dudeku/esp-now-differential-probe/scripts/graphs/0_5_GeV.png

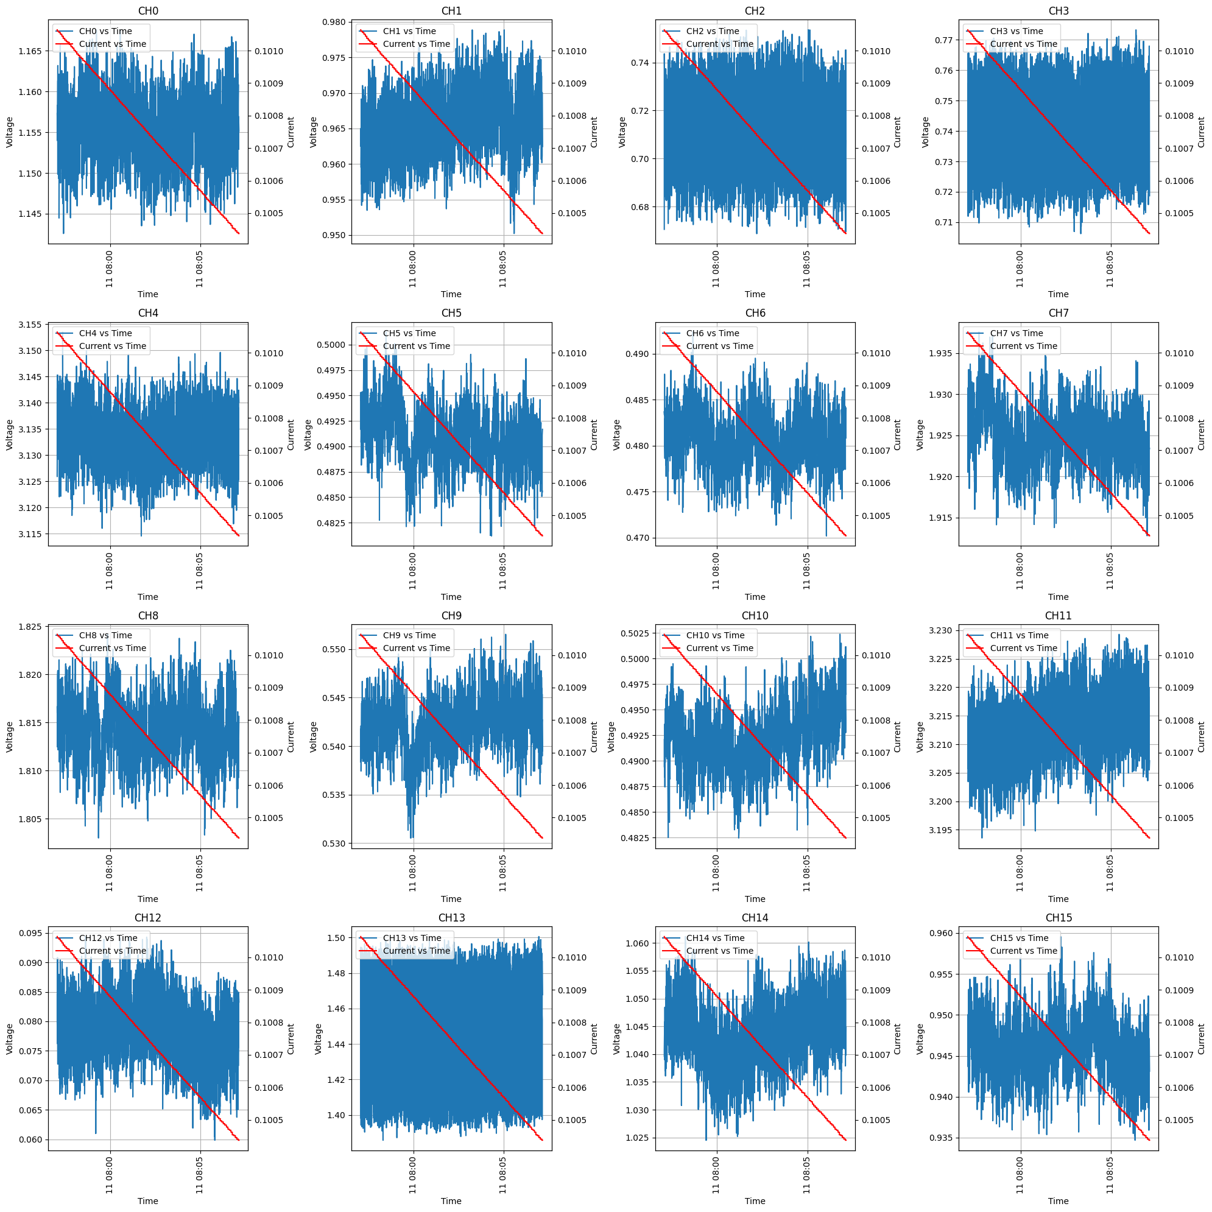
scripts/graphs/0_5_GeV.png
