dudeku/esp-now-differential-probe/scripts/graphs/espsonda_08-06-30_27-02-2025_1.png

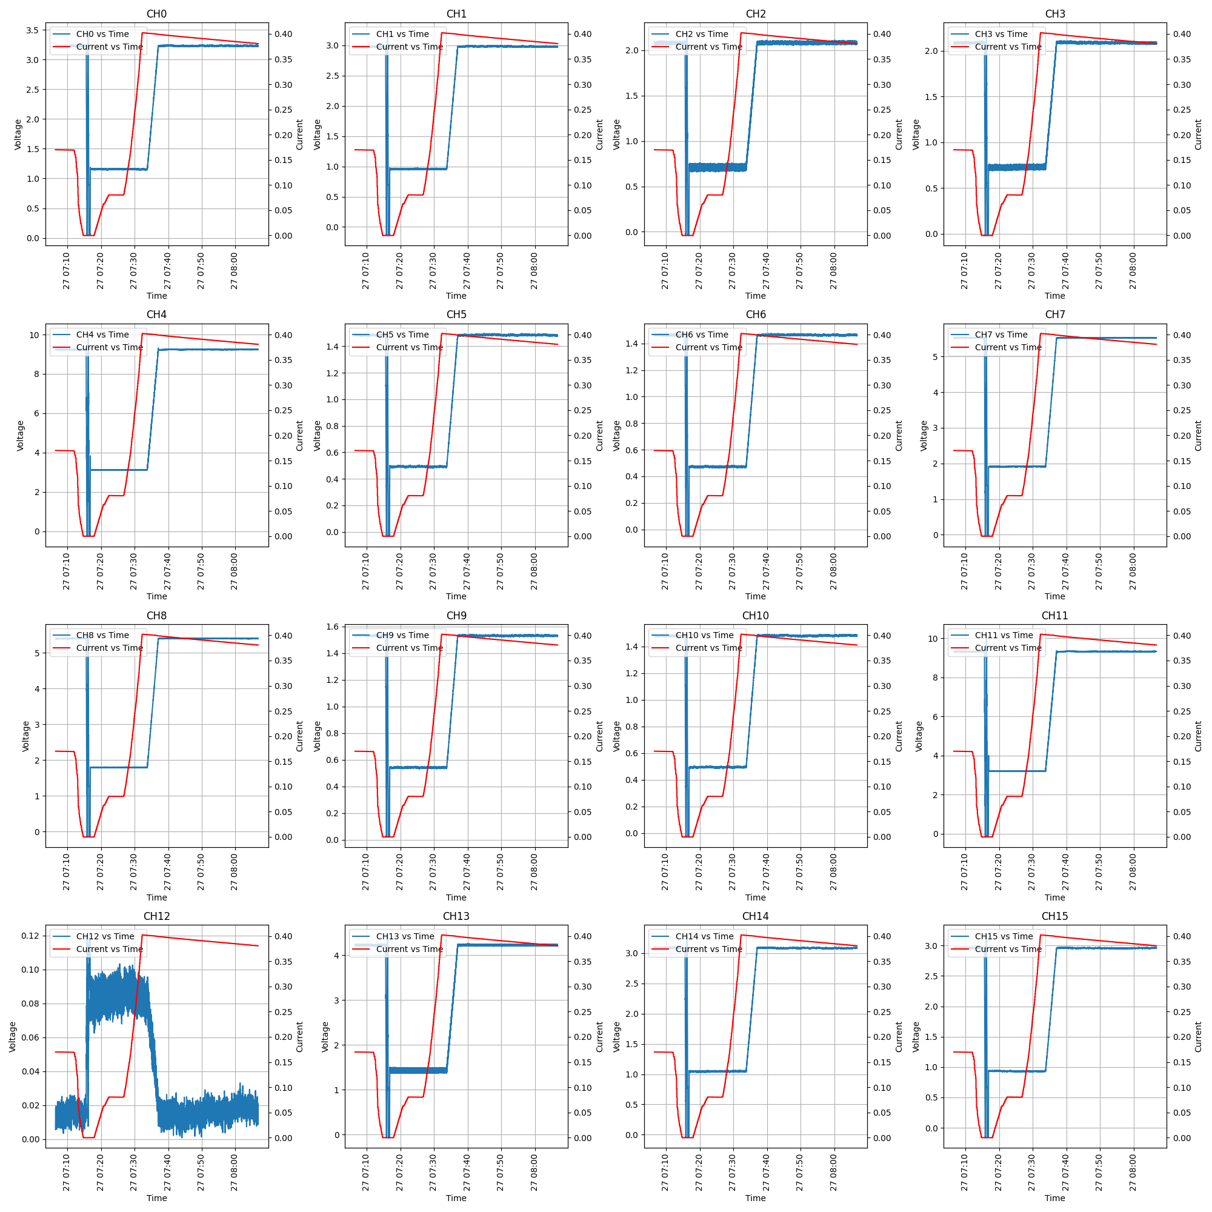
scripts/graphs/espsonda_08-06-30_27-02-2025_1.png
