dudeku/esp-now-differential-probe/scripts/graphs/espsonda_08-07-44_05-06-2025_2.png

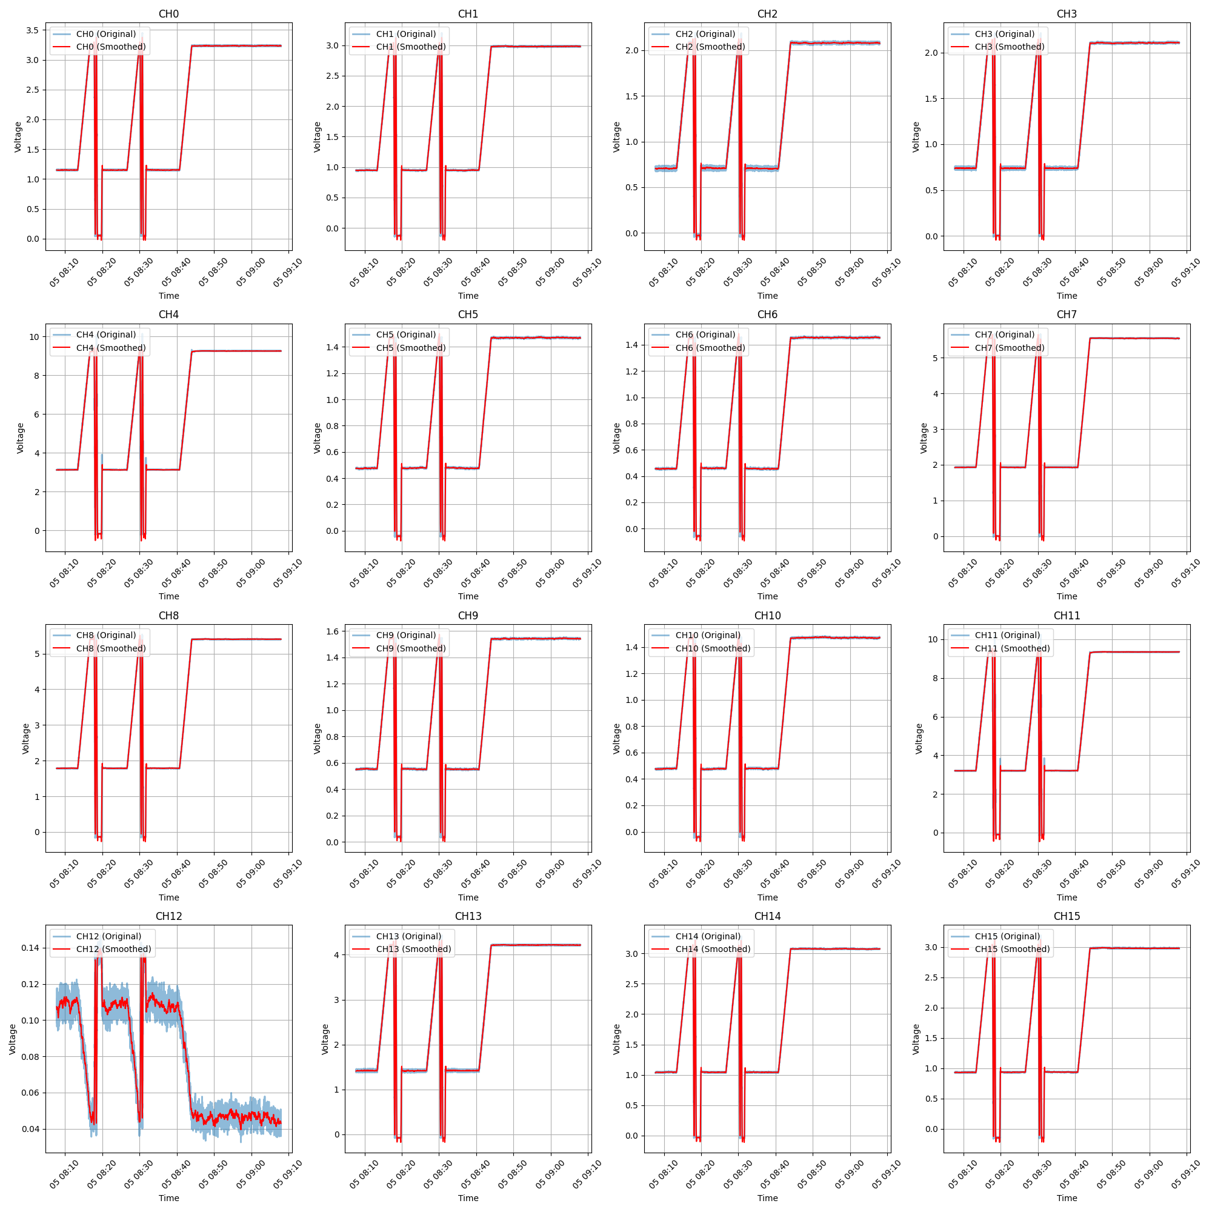
scripts/graphs/espsonda_08-07-44_05-06-2025_2.png
