dudeku/esp-now-differential-probe/scripts/graphs/espsonda_09-22-08_12-12-2025_fig3.png

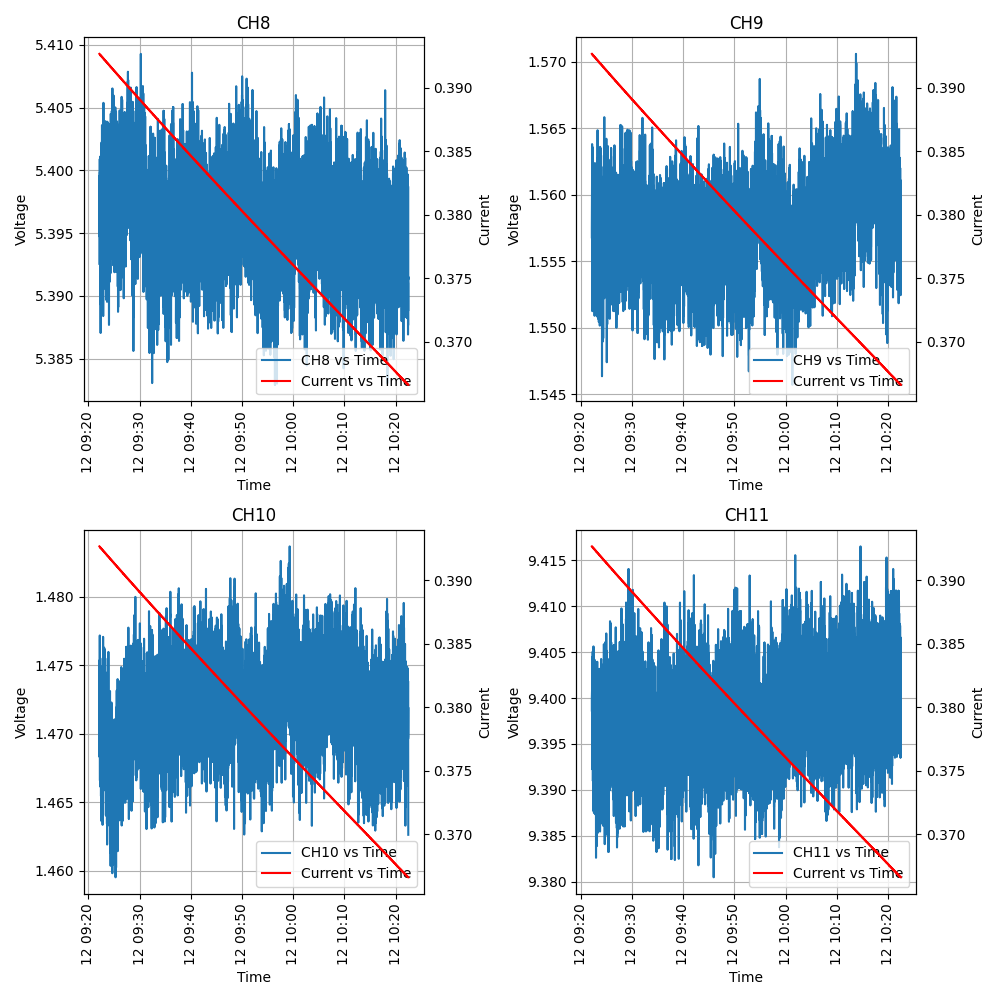
scripts/graphs/espsonda_09-22-08_12-12-2025_fig3.png
