dudeku/esp-now-differential-probe/scripts/graphs/espsonda_10-20-50_02-06-2025_2.png

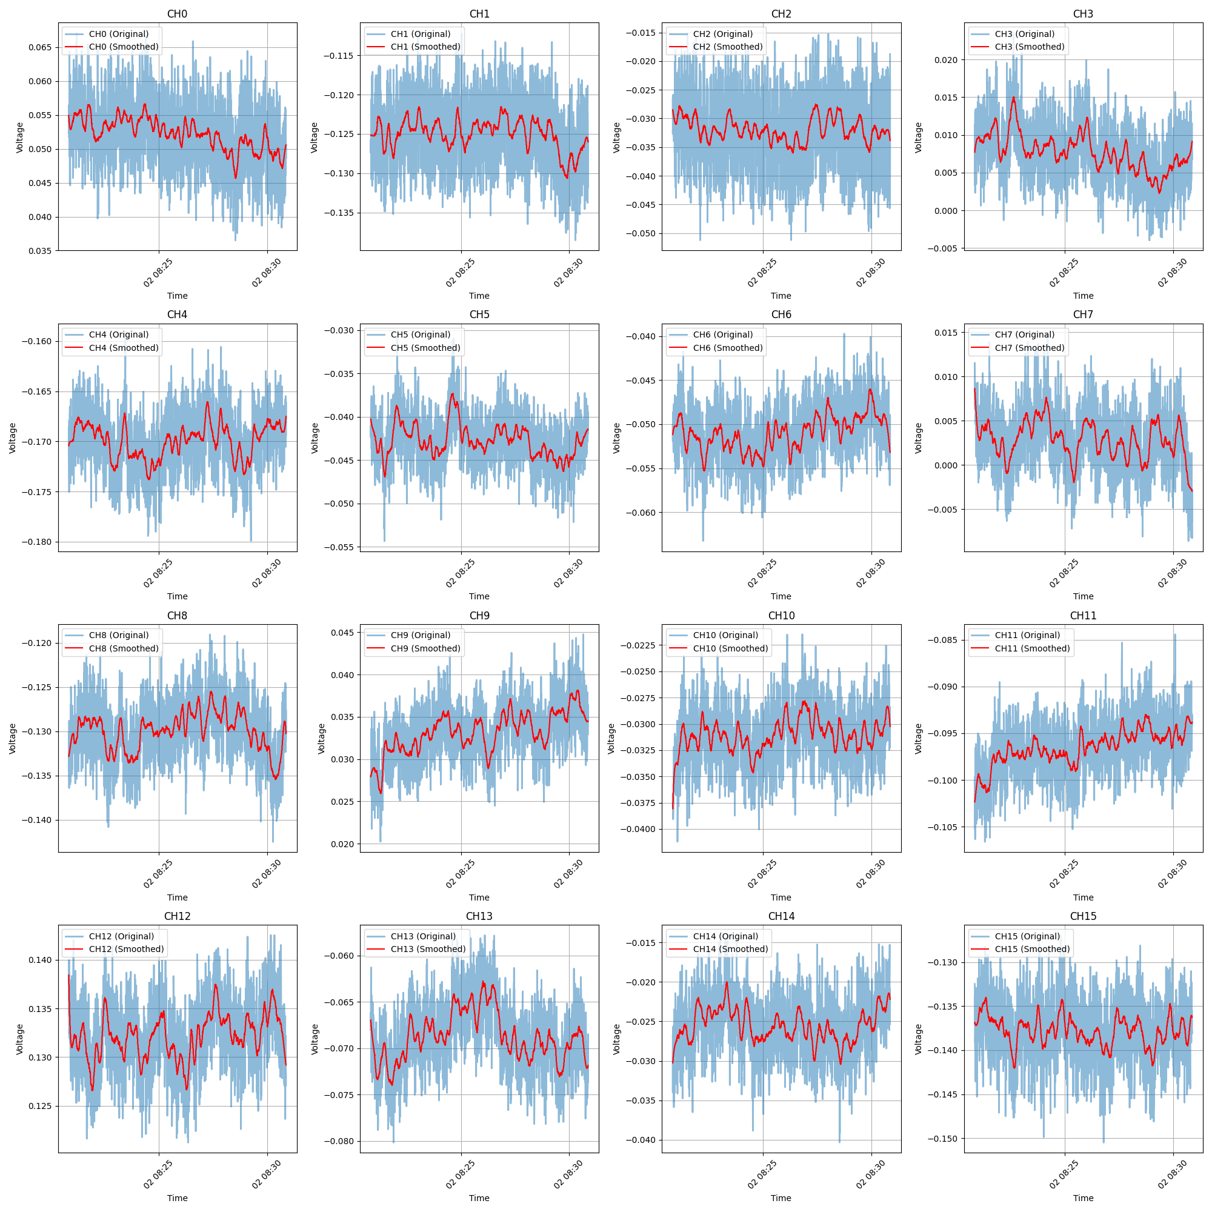
scripts/graphs/espsonda_10-20-50_02-06-2025_2.png
