dudeku/esp-now-differential-probe/scripts/graphs/espsonda_10-25-32_25-02-2025_2.png

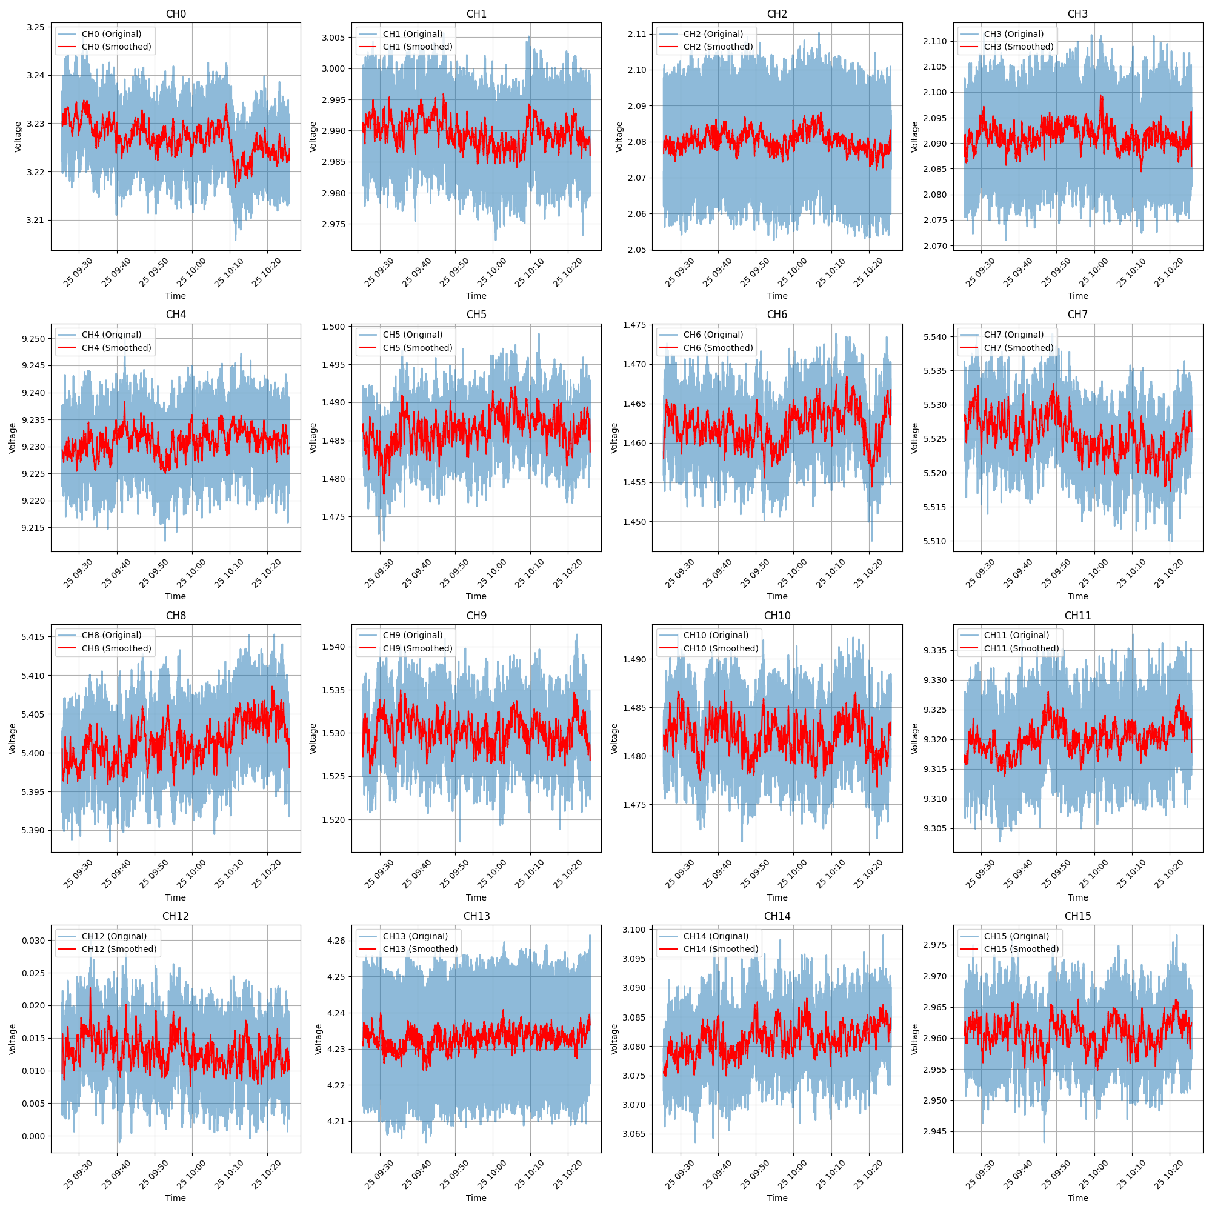
scripts/graphs/espsonda_10-25-32_25-02-2025_2.png
