dudeku/esp-now-differential-probe/scripts/graphs/espsonda_11-54-26_20-05-2025_2.png

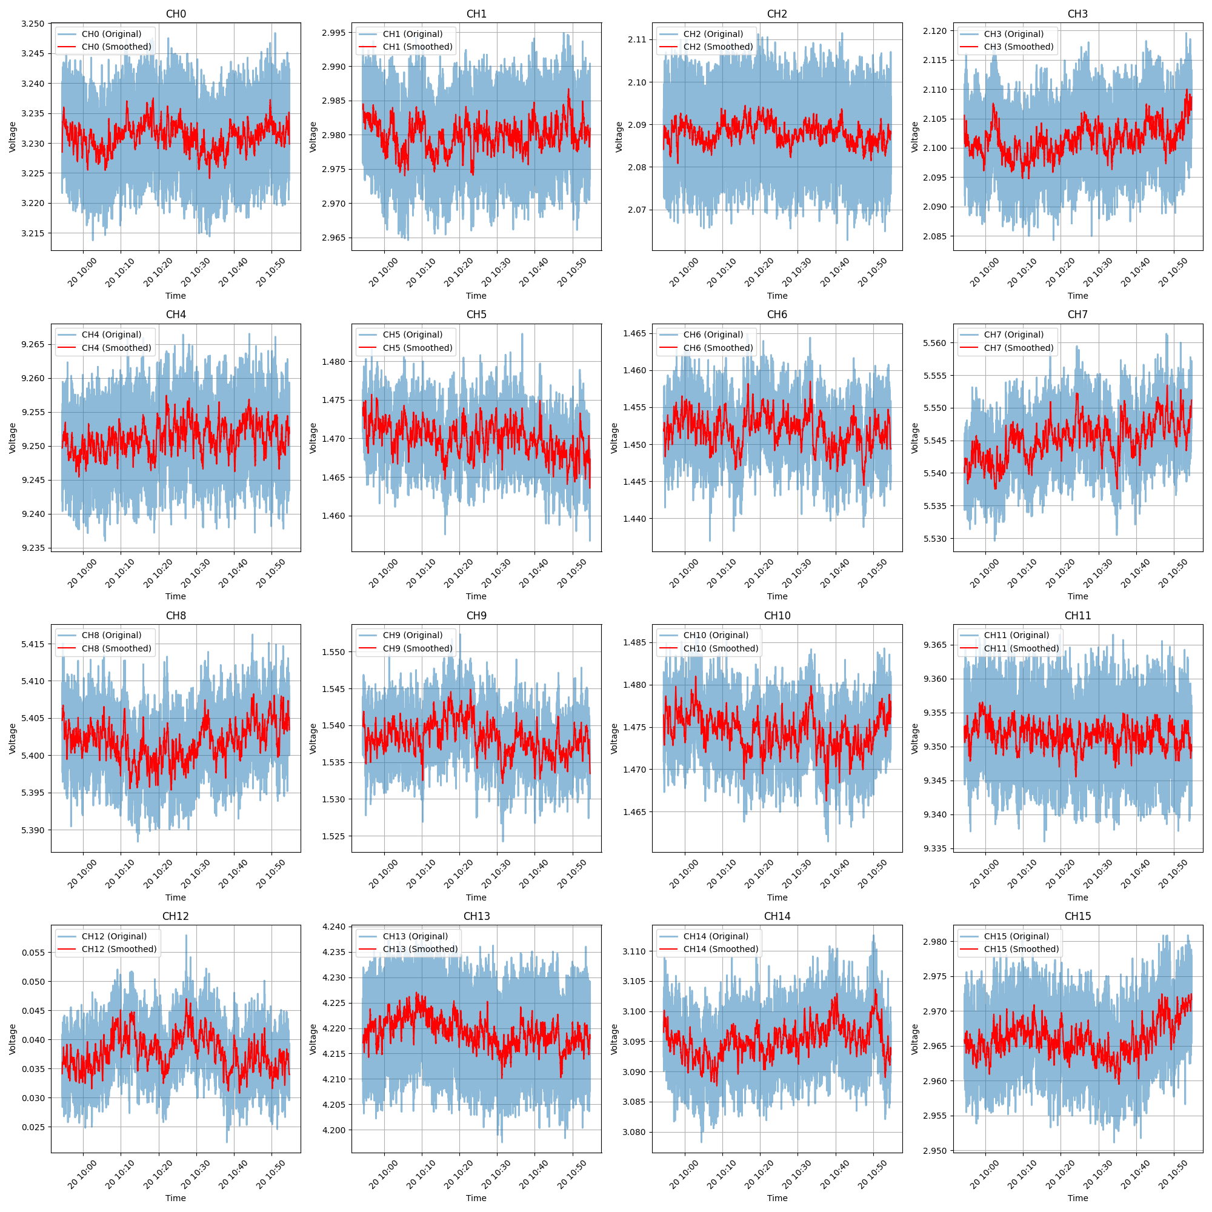
scripts/graphs/espsonda_11-54-26_20-05-2025_2.png
