dudeku/esp-now-differential-probe/scripts/graphs/espsonda_12-19-58_25-02-2025_1.png

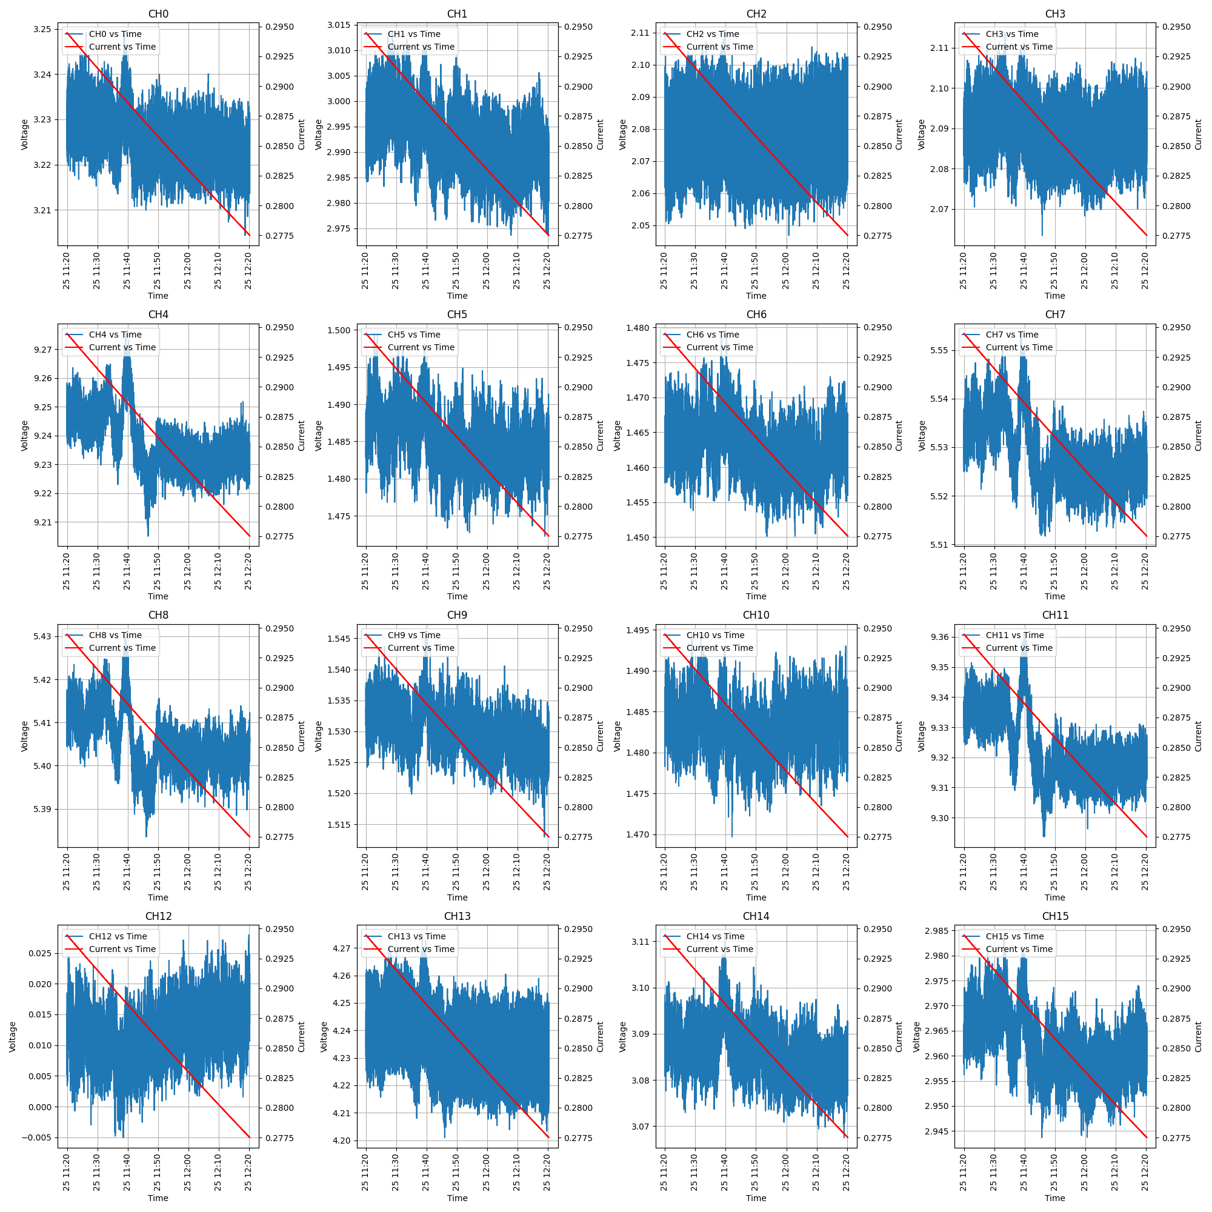
scripts/graphs/espsonda_12-19-58_25-02-2025_1.png
