dudeku/esp-now-differential-probe/scripts/graphs/espsonda_12-19-58_25-02-2025_2.png

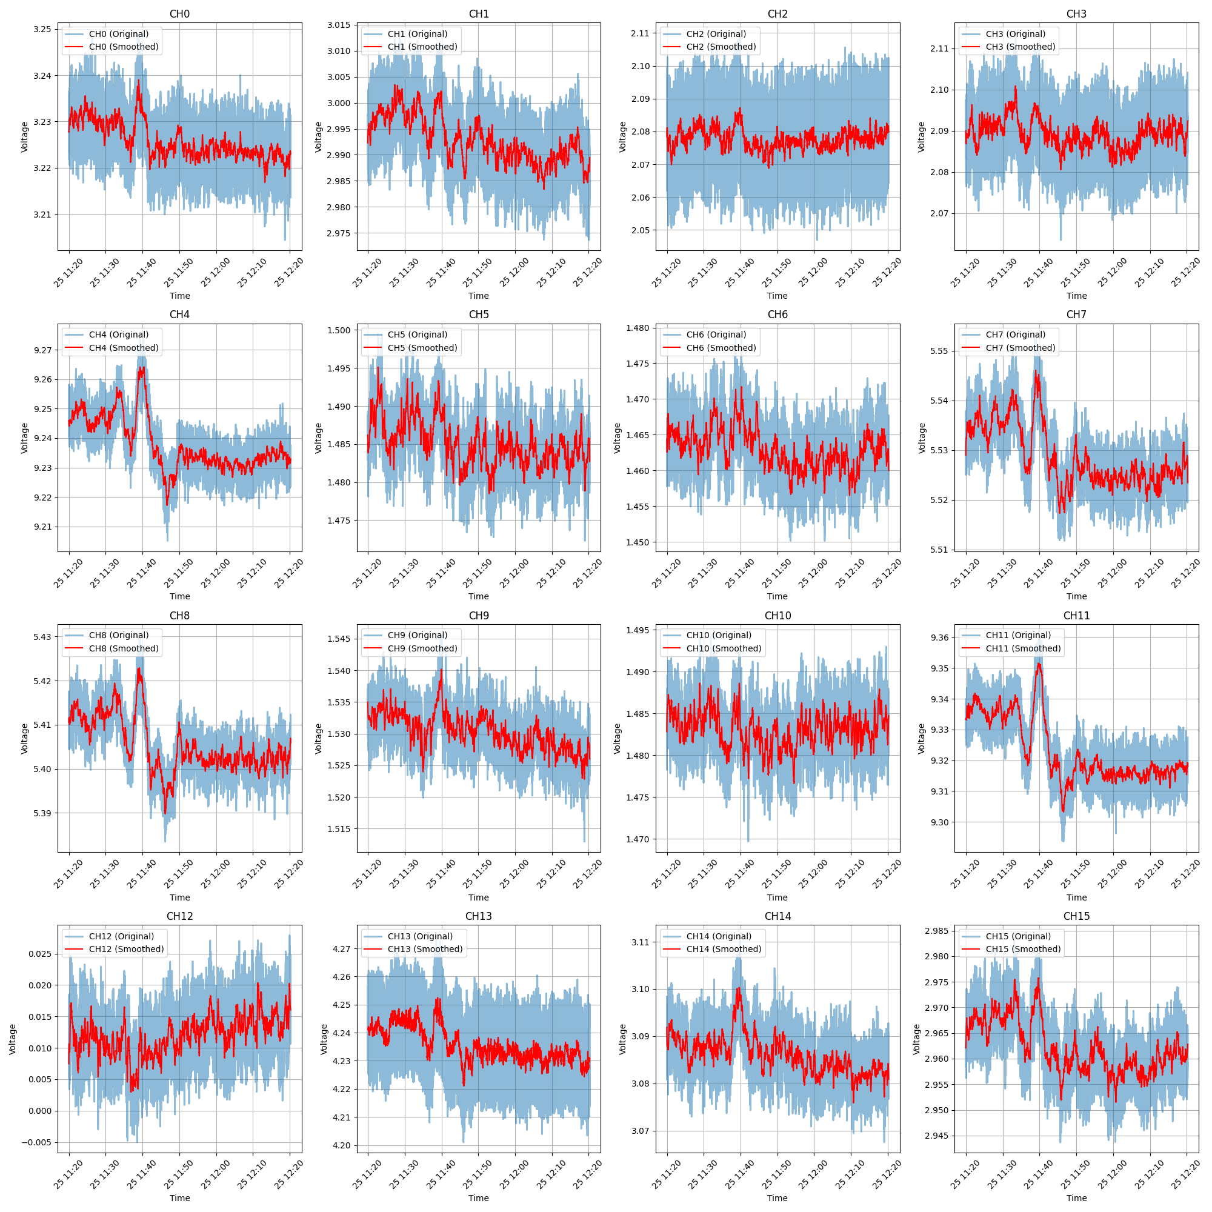
scripts/graphs/espsonda_12-19-58_25-02-2025_2.png
