dudeku/esp-now-differential-probe/scripts/graphs/espsonda_13-14-20_18-02-2025_2.png

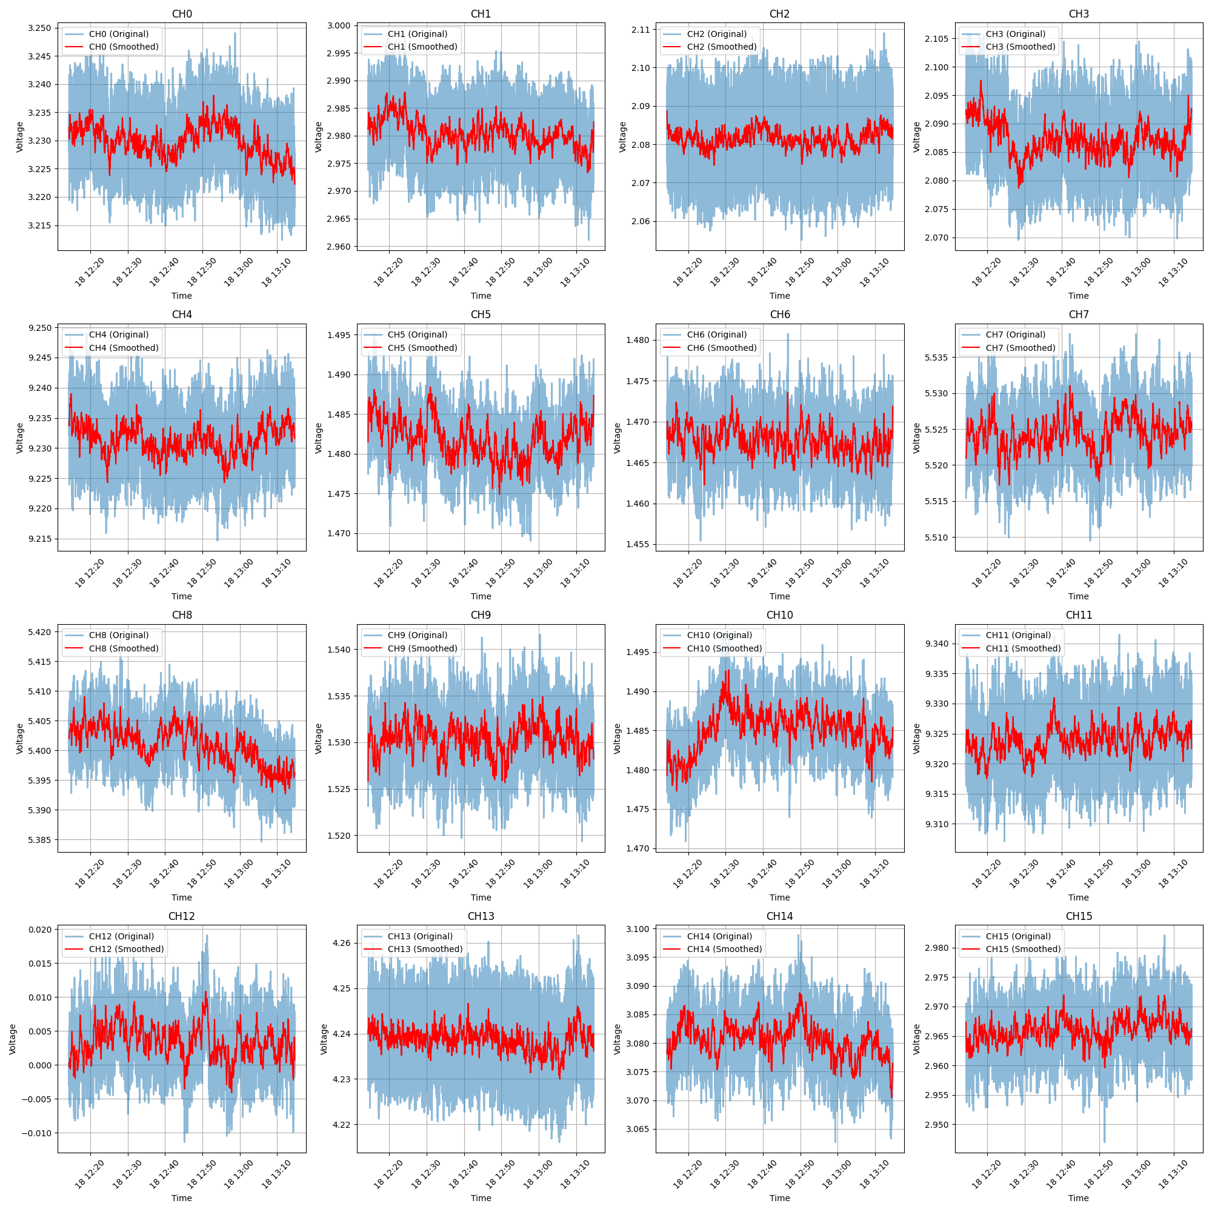
scripts/graphs/espsonda_13-14-20_18-02-2025_2.png
