dudeku/esp-now-differential-probe/scripts/graphs/espsonda_13-39-03_02-06-2025_1.png

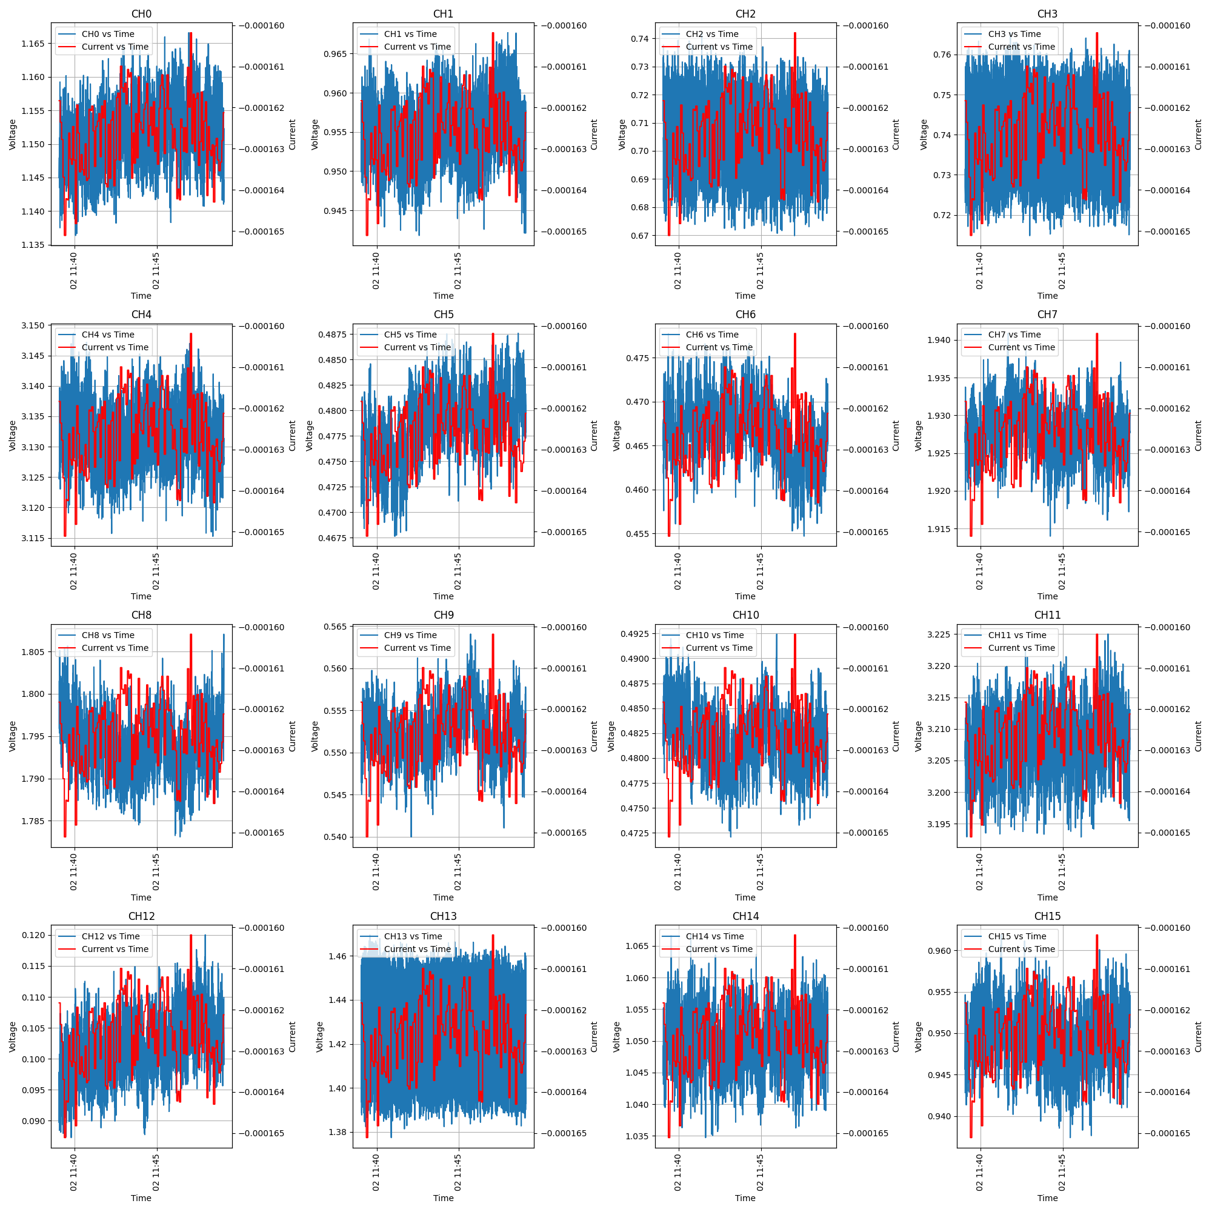
scripts/graphs/espsonda_13-39-03_02-06-2025_1.png
