dudeku/esp-now-differential-probe/scripts/measurements/1hr_measurement_smoothed.png

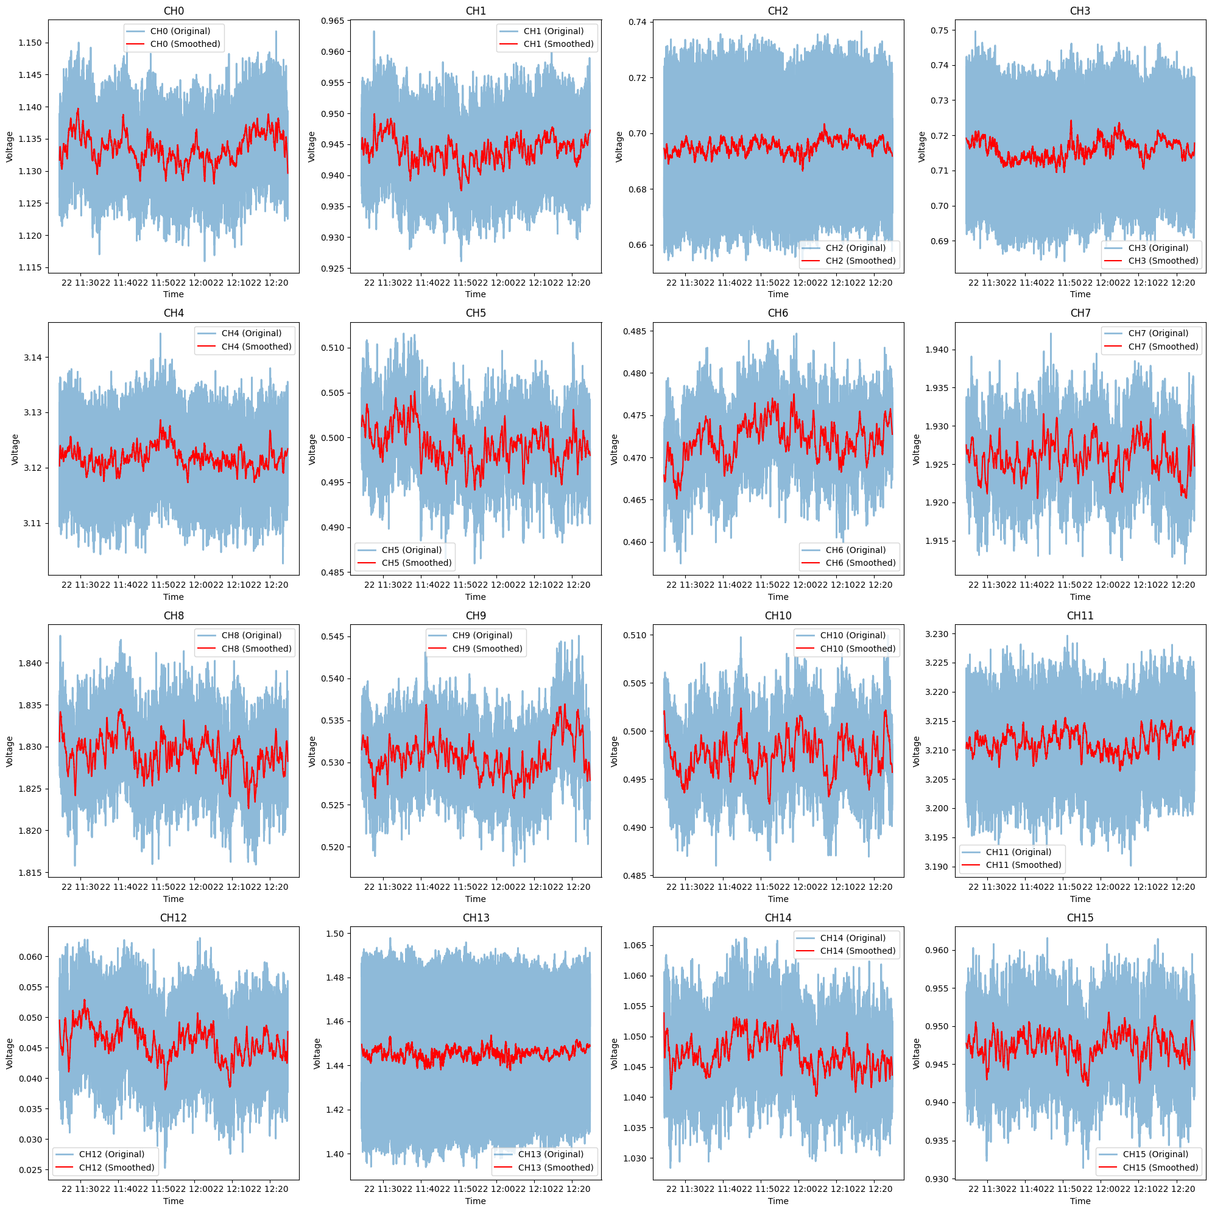
scripts/measurements/1hr_measurement_smoothed.png
