dudeku/esp-now-differential-probe/scripts/measurements/24_01_ramping_with_pause_mid-ramp.png

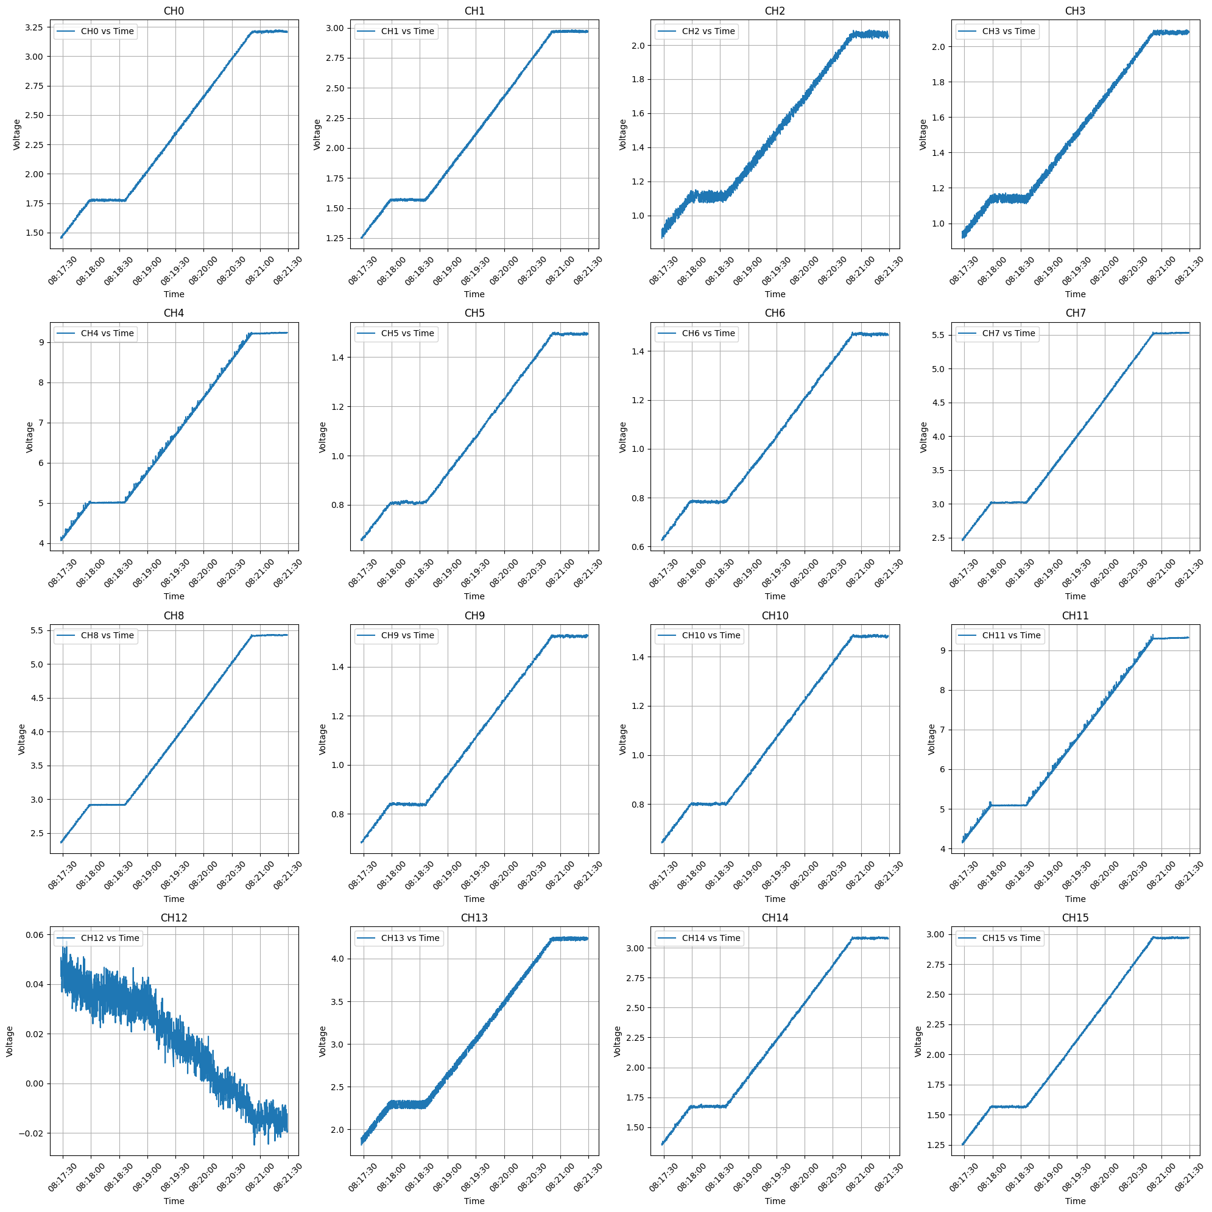
scripts/measurements/24_01_ramping_with_pause_mid-ramp.png
