dudeku/esp-now-differential-probe/simluation/ltc6268_probe.asc

C1: cap; 0.25p
C2: cap; 0.25p
C3: cap; 0.8p
C4: cap; 6.8p
C5: cap; 6.8p
C6: cap; 470µ
R1: res; 5Meg
R2: res; 5Meg
R3: res; 10020
R4: res; 10020
R5: res; 470
R6: res; 470
R7: res; 348
R8: res; 348
R9: res; 348
R10: res; 1k
R11: res; 150
R12: res; 150
R13: res; 150
R14: res; 150
R15: res; 16
R16: res; 348
R17: res; 470
U1: LTC6268
U2: LTC6268
U3: LMH6611
V1: voltage; SINE(250 9 10000)
V2: voltage; 240
V3: voltage; 2.5
V4: voltage; 2.5
Named nets: 0, 2.5V, -2.5V, out, IN1, IN2
.dc V1 210 270 1
.noise V(out) V1  lin 101 0.1 1k
.tran 0 10m 0 1u
